bjkayani/PCB-Reflow-Hot-Plate/Test Data/Thermal Testing/plate_fr4-pcb_1.6mm.csv

Channel 1 | Channel 2
0 | 0
0 | 0
0 | 0
0 | 0
0 | 0
0 | 0
0 | 0
0 | 0
0 | 0
0 | 0
0 | 0
0 | 0
0 | 0
0 | 0
0 | 0
0 | 0
0 | 0
0 | 0
0 | 0
0 | 0
0 | 0
0 | 0
0 | 0
0 | 0
0 | 0
0 | 0
0 | 0
0 | 0
0 | 0
0 | 0
0 | 0
0 | 0
0 | 0
0 | 0
0 | 0
0 | 0
0 | 0
0 | 0
0 | 0
0 | 0
0 | 0
0 | 0
0 | 0
0 | 0
0 | 0
0 | 0
0 | 0
0 | 0
0 | 0
0 | 0
0 | 0
0 | 0
0 | 0
0 | 0
0 | 0
0 | 0
0 | 0
0 | 0
0 | 0
0 | 0
0 | 0
0 | 0
0 | 0
0 | 0
0 | 0
0 | 0
0 | 0
0 | 0
0 | 0
0 | 0
0 | 0
0 | 0
0 | 0
0 | 0
0 | 0
0 | 0
0 | 0
0 | 0
0 | 0
0 | 0
0 | 0
0 | 0
0 | 0
0 | 0
0 | 0
0 | 0
0 | 0
0 | 0
0 | 0
0 | 0
0 | 0
0 | 0
0 | 0
0 | 0
0 | 0
0 | 0
0 | 0
0 | 0
0 | 0
0 | 0
0 | 0
0 | 0
0 | 0
0 | 0
0 | 0
0 | 0
0 | 0
0 | 0
0 | 0
0 | 0
0 | 0
0 | 0
0 | 0
0 | 0
0 | 0
0 | 0
0 | 0
0 | 0
0 | 0
0 | 0
0 | 0
0 | 0
0 | 0
0 | 0
0 | 0
0 | 0
0 | 0
0 | 0
0 | 0
0 | 0
0 | 0
0 | 0
0 | 0
0 | 0
0 | 0
0 | 0
0 | 0
0 | 0
0 | 0
0 | 0
0 | 0
0 | 0
0 | 0
0 | 0
0 | 0
0 | 0
0 | 0
0 | 0
0 | 0
0 | 0
0 | 0
0 | 0
0 | 0
0 | 0
0 | 0
0 | 0
0 | 0
0 | 0
0 | 0
0 | 0
0 | 0
0 | 0
0 | 0
0 | 0
0 | 0
0 | 0
0 | 0
0 | 0
0 | 0
0 | 0
0 | 0
0 | 0
0 | 0
0 | 0
0 | 0
0 | 0
0 | 0
0 | 0
0 | 0
0 | 0
0 | 0
0 | 0
0 | 0
0 | 0
0 | 0
0 | 0
0 | 0
0 | 0
0 | 0
0 | 0
0 | 0
0 | 0
0 | 0
0 | 0
0 | 0
0 | 0
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
