bjkayani/PCB-Reflow-Hot-Plate/Test Data/Thermal Testing/top-ir-20mm-thrmcpl.csv

Channel 1 | Channel 2 | Channel 3
0 | 0 | 0
0 | 0 | 0
0 | 0 | 0
0 | 0 | 0
0 | 0 | 0
0 | 0 | 0
0 | 0 | 0
0 | 0 | 0
0 | 0 | 0
0 | 0 | 0
0 | 0 | 0
0 | 0 | 0
0 | 0 | 0
0 | 0 | 0
0 | 0 | 0
0 | 0 | 0
0 | 0 | 0
0 | 0 | 0
0 | 0 | 0
0 | 0 | 0
0 | 0 | 0
0 | 0 | 0
0 | 0 | 0
0 | 0 | 0
0 | 0 | 0
0 | 0 | 0
0 | 0 | 0
0 | 0 | 0
0 | 0 | 0
0 | 0 | 0
0 | 0 | 0
0 | 0 | 0
0 | 0 | 0
0 | 0 | 0
0 | 0 | 0
0 | 0 | 0
0 | 0 | 0
0 | 0 | 0
0 | 0 | 0
0 | 0 | 0
0 | 0 | 0
0 | 0 | 0
0 | 0 | 0
0 | 0 | 0
0 | 0 | 0
0 | 0 | 0
0 | 0 | 0
0 | 0 | 0
0 | 0 | 0
0 | 0 | 0
0 | 0 | 0
0 | 0 | 0
0 | 0 | 0
0 | 0 | 0
0 | 0 | 0
0 | 0 | 0
0 | 0 | 0
0 | 0 | 0
0 | 0 | 0
0 | 0 | 0
0 | 0 | 0
0 | 0 | 0
0 | 0 | 0
0 | 0 | 0
0 | 0 | 0
0 | 0 | 0
0 | 0 | 0
0 | 0 | 0
0 | 0 | 0
0 | 0 | 0
0 | 0 | 0
0 | 0 | 0
0 | 0 | 0
0 | 0 | 0
0 | 0 | 0
0 | 0 | 0
0 | 0 | 0
0 | 0 | 0
0 | 0 | 0
0 | 0 | 0
0 | 0 | 0
0 | 0 | 0
0 | 0 | 0
0 | 0 | 0
0 | 0 | 0
0 | 0 | 0
0 | 0 | 0
0 | 0 | 0
0 | 0 | 0
0 | 0 | 0
0 | 0 | 0
0 | 0 | 0
0 | 0 | 0
0 | 0 | 0
0 | 0 | 0
0 | 0 | 0
0 | 0 | 0
0 | 0 | 0
0 | 0 | 0
0 | 0 | 0
0 | 0 | 0
0 | 0 | 0
0 | 0 | 0
0 | 0 | 0
0 | 0 | 0
0 | 0 | 0
0 | 0 | 0
0 | 0 | 0
0 | 0 | 0
0 | 0 | 0
0 | 0 | 0
0 | 0 | 0
0 | 0 | 0
0 | 0 | 0
0 | 0 | 0
0 | 0 | 0
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
