bjkayani/PCB-Reflow-Hot-Plate/Code/pcb-reflow-hot-plate/bitmaps.ino

/**
 * PCB Reflow Hot Plate
 * bitmaps.ino 
 * Saved bitmaps for the display
 */

const unsigned char bw_logo_70_39 [] PROGMEM = {
	// 'Logo Bitmap, 70x39px
	0x7f, 0xff, 0xe0, 0x03, 0x00, 0x00, 0x00, 0x1f, 0xfc, 0x7f, 0xff, 0xfc, 0x03, 0x80, 0x18, 0x00, 
	0x1f, 0xfc, 0x7f, 0xff, 0xff, 0x03, 0x80, 0x3c, 0x00, 0x1f, 0xf8, 0x70, 0x00, 0x1f, 0x83, 0xc0, 
	0x3c, 0x00, 0x3c, 0x78, 0x70, 0x00, 0x07, 0xc1, 0xc0, 0x7c, 0x00, 0x38, 0x78, 0x70, 0x00, 0x01, 
	0xe1, 0xc0, 0x7e, 0x00, 0x38, 0x78, 0x71, 0xff, 0xe0, 0xe1, 0xc0, 0x7e, 0x00, 0x78, 0x70, 0xf9, 
	0xff, 0xf8, 0xf1, 0xe0, 0xff, 0x00, 0x70, 0x70, 0x89, 0xff, 0xfc, 0x70, 0xe0, 0xe7, 0x00, 0x70, 
	0xf0, 0xd9, 0xc0, 0x3c, 0x70, 0xf1, 0xe7, 0x00, 0x71, 0xf0, 0x71, 0x80, 0x1c, 0x78, 0x91, 0xc3, 
	0x80, 0xf1, 0x10, 0x70, 0x00, 0x1c, 0x78, 0x99, 0xc3, 0x80, 0xe1, 0xb0, 0x70, 0x00, 0x1c, 0x78, 
	0xf0, 0x03, 0xc0, 0xe1, 0xe0, 0x70, 0x00, 0x3c, 0x78, 0x78, 0x01, 0xc0, 0xe1, 0xe0, 0x7f, 0xff, 
	0xfe, 0xfc, 0x38, 0x01, 0xc1, 0xe1, 0xc0, 0x7f, 0xff, 0xff, 0xfc, 0x38, 0x01, 0xe1, 0xc1, 0xc0, 
	0x7f, 0xff, 0xff, 0xfc, 0x3c, 0x00, 0xe1, 0xc3, 0xc0, 0x00, 0x00, 0x01, 0xfe, 0x3c, 0x00, 0xe0, 
	0x83, 0xc0, 0x00, 0x00, 0x30, 0x7e, 0x1c, 0x00, 0xf0, 0x03, 0x80, 0x00, 0x00, 0x36, 0x3e, 0x1c, 
	0x18, 0x70, 0x03, 0x80, 0x71, 0xff, 0xfe, 0x1f, 0x1e, 0x38, 0x78, 0x03, 0x80, 0x71, 0xff, 0xfe, 
	0x1f, 0x0c, 0x38, 0x7c, 0x07, 0x00, 0x71, 0xff, 0xff, 0xcf, 0x00, 0x78, 0x44, 0x07, 0x00, 0x71, 
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
	0x40, 0x0c, 0xe3, 0x03, 0x30, 0x4f, 0xfd, 0xf3, 0x03, 0x30, 0x40, 0x39, 0xb6, 0x01, 0xa0, 0x40, 
	0x07, 0x3e, 0x01, 0xe0, 0x7f, 0xfe, 0x1c, 0x01, 0xe0, 0x7f, 0xf8, 0x1c, 0x00, 0xc0, 0x00, 0x00, 
	0x00, 0x00, 0x00
};
